saikhamhein/benchswitch-usb-dut-hub/PCB/models/nominal/SPZ1HM221G12O00RAXXX_nominal.step

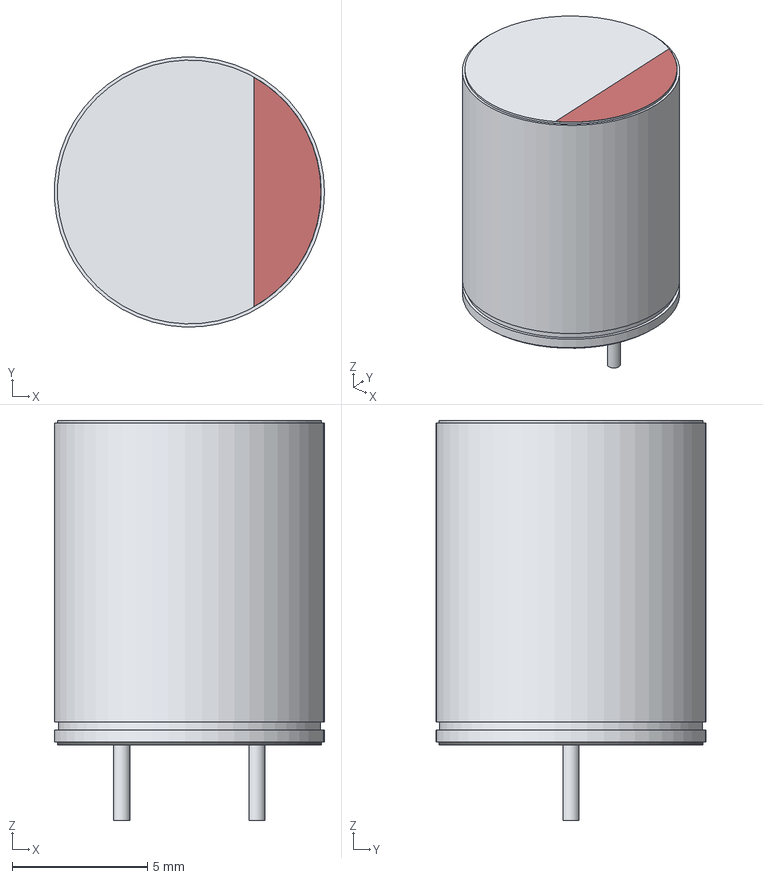
[picture p16: CAD file, 2026-10-05]
PCB/models/nominal/SPZ1HM221G12O00RAXXX_nominal.step
9.99 x 10.00 x 14.8 mm
Aluminum_can
Bottom_bung
Top_lid
Negative_polarity_red_sector
Lead_1_positive
Lead_2_negative
