saikhamhein/benchswitch-usb-dut-hub/PCB/models/nominal/XL1EL89CSI_111YLC_24M_nominal.step

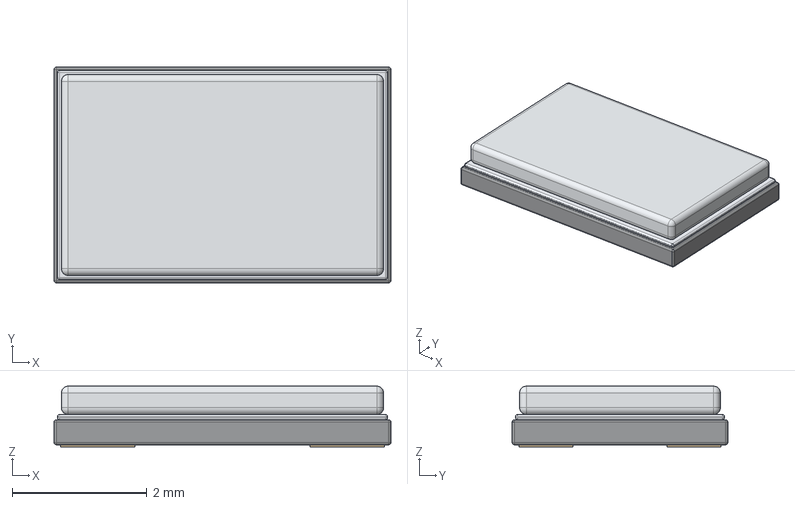
[picture p17: CAD file, 2026-10-05]
PCB/models/nominal/XL1EL89CSI_111YLC_24M_nominal.step
5.00 x 3.20 x 0.9 mm
Ceramic_base
Metal_sealing_flange
Metal_lid_no_text
Gold_terminal_1
Gold_terminal_2
Gold_terminal_3
Gold_terminal_4
