saikhamhein/benchswitch-usb-dut-hub/PCB/models/nominal/CL10C330JB8NNNC_nominal.step

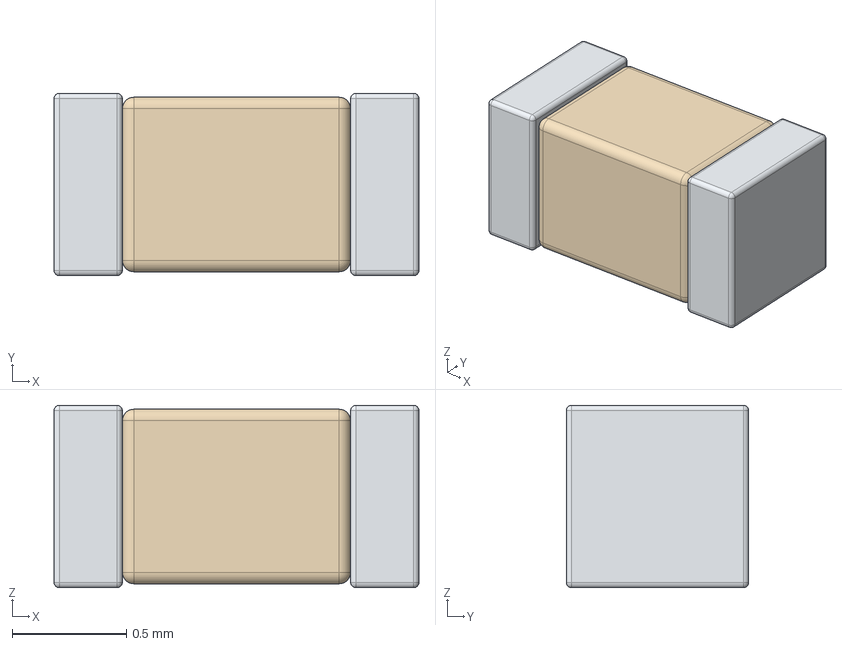
[picture p18: CAD file, 2026-10-05]
PCB/models/nominal/CL10C330JB8NNNC_nominal.step
1.60 x 0.8 x 0.8 mm
Ceramic_nominal
Termination_1
Termination_2
