saikhamhein/benchswitch-usb-dut-hub/PCB/models/nominal/MNR8065T100MT_nominal.step

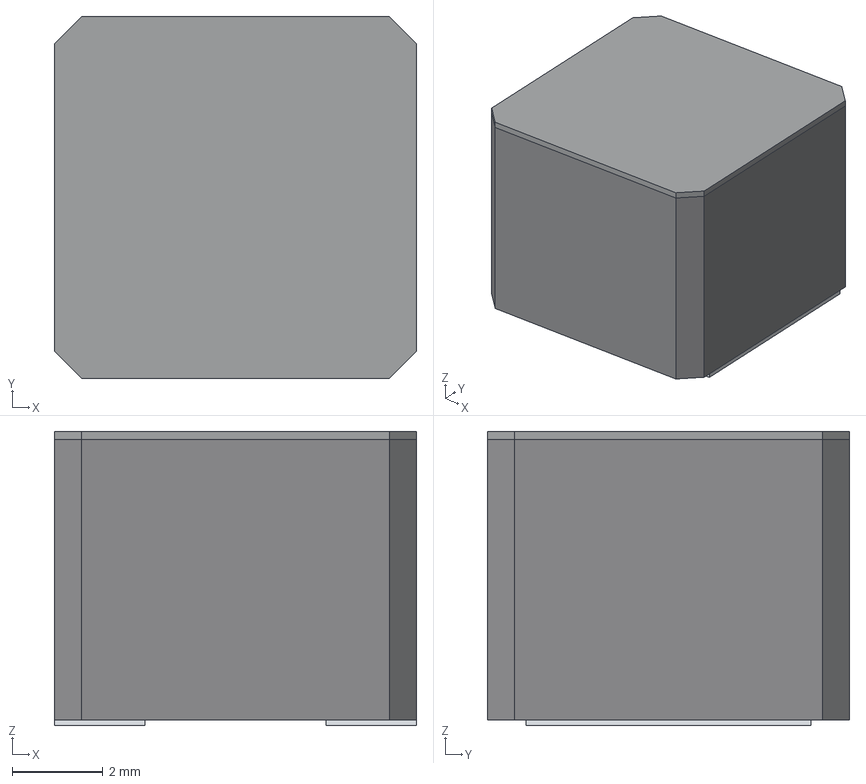
[picture p19: CAD file, 2026-10-05]
PCB/models/nominal/MNR8065T100MT_nominal.step
8.00 x 8.00 x 6.50 mm
Magnetic_resin_body_nominal_XY_max_H
Ferrite_top_face
Tin_terminal_1
Tin_terminal_2
