saikhamhein/benchswitch-usb-dut-hub/PCB/models/nominal/RC0603_RT0603_nominal.step

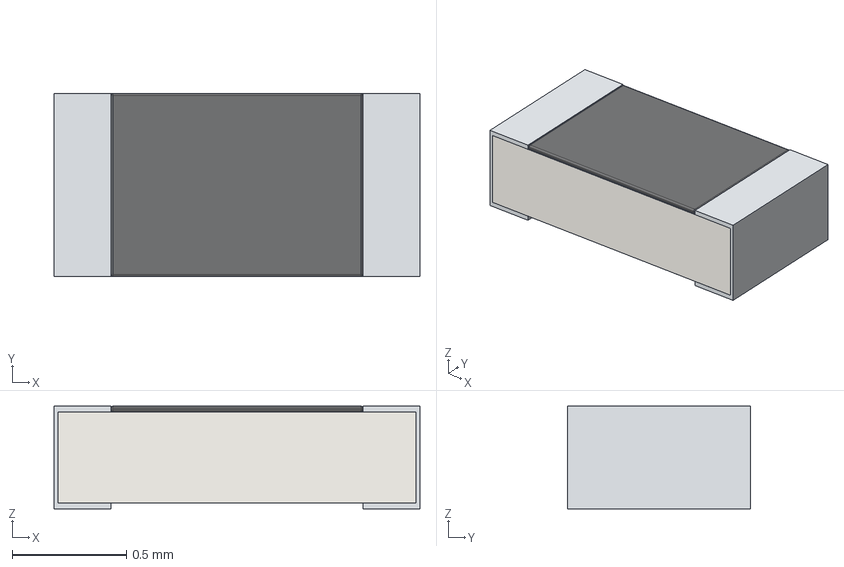
[picture p20: CAD file, 2026-10-05]
PCB/models/nominal/RC0603_RT0603_nominal.step
1.60 x 0.8 x 0.45 mm
Alumina_substrate
Resistive_overcoat_no_text
Termination_1
Termination_2
