saikhamhein/benchswitch-usb-dut-hub/PCB/models/nominal/CH217A_family_nominal.step

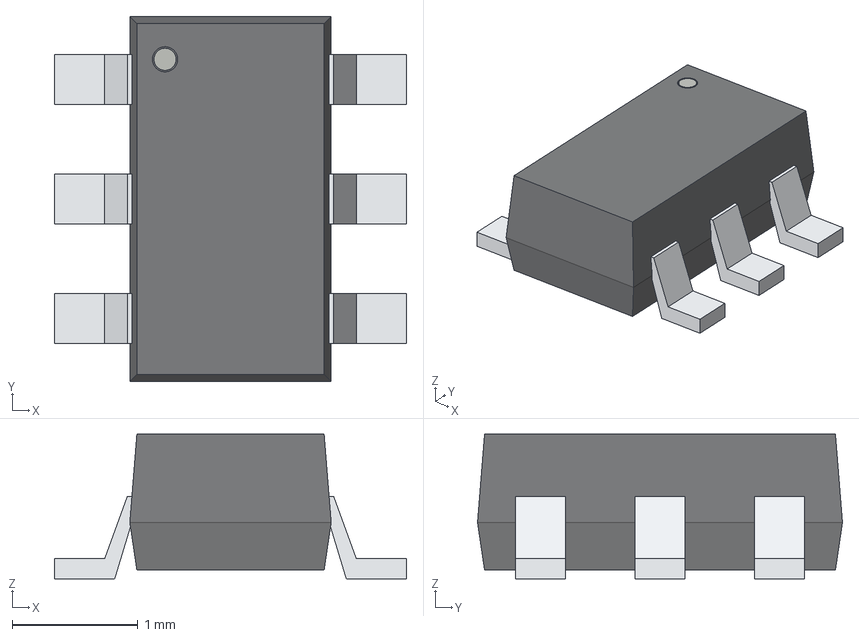
[picture p21: CAD file, 2026-10-05]
PCB/models/nominal/CH217A_family_nominal.step
2.80 x 2.90 x 1.15 mm
Pin1_orientation_dot_schematic
Molded_body
Lead_1
Lead_2
Lead_3
Lead_4
Lead_5
Lead_6
