saikhamhein/benchswitch-usb-dut-hub/PCB/models/nominal/CC0805KKX7R7BB106_nominal.step

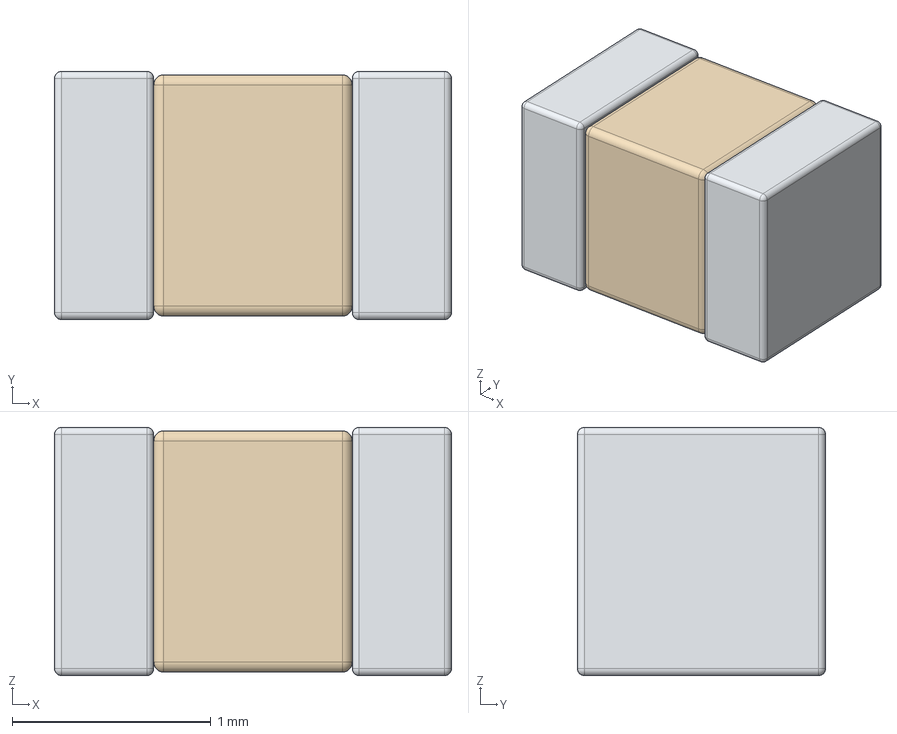
[picture p22: CAD file, 2026-10-05]
PCB/models/nominal/CC0805KKX7R7BB106_nominal.step
2.00 x 1.25 x 1.25 mm
Ceramic_nominal
Termination_1
Termination_2
