saikhamhein/benchswitch-usb-dut-hub/PCB/models/nominal/LTST_S270KGKT_sideview_nominal.step

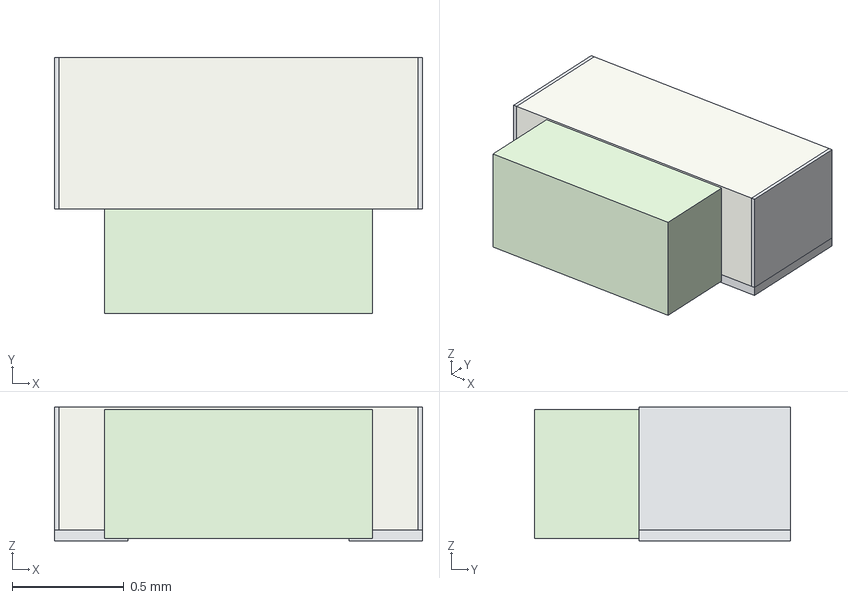
[picture p23: CAD file, 2026-10-05]
PCB/models/nominal/LTST_S270KGKT_sideview_nominal.step
1.65 x 1.15 x 0.6 mm
Ceramic_package
Cathode_1
Cathode_end
Anode_2
Anode_end
Water_clear_side_lens
Green_die_behind_lens
Cathode_underside_mark
