saikhamhein/benchswitch-usb-dut-hub/PCB/models/nominal/USB2514B_AEZC_QFN36_nominal.step

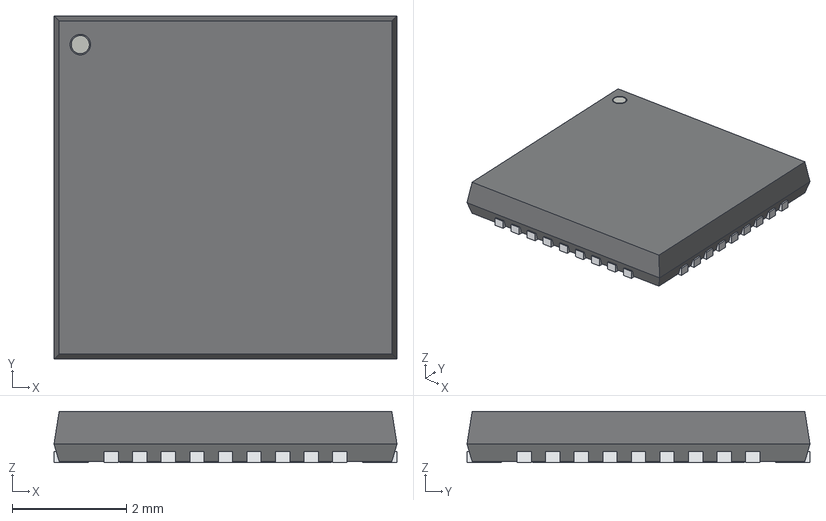
[picture p24: CAD file, 2026-10-05]
PCB/models/nominal/USB2514B_AEZC_QFN36_nominal.step
6.00 x 6.00 x 0.9 mm
Pin1_orientation_dot_schematic
Molded_body
Exposed_pad_37
Terminal_1
Terminal_10
Terminal_19
Terminal_28
Terminal_2
Terminal_11
Terminal_20
Terminal_29
Terminal_3
Terminal_12
Terminal_21
Terminal_30
Terminal_4
Terminal_13
Terminal_22
Terminal_31
Terminal_5
Terminal_14
Terminal_23
Terminal_32
Terminal_6
Terminal_15
Terminal_24
Terminal_33
Terminal_7
Terminal_16
Terminal_25
Terminal_34
Terminal_8
Terminal_17
Terminal_26
Terminal_35
Terminal_9
Terminal_18
Terminal_27
Terminal_36
