saikhamhein/benchswitch-usb-dut-hub/PCB/models/nominal/ERS1AM221E11OT_nominal.step

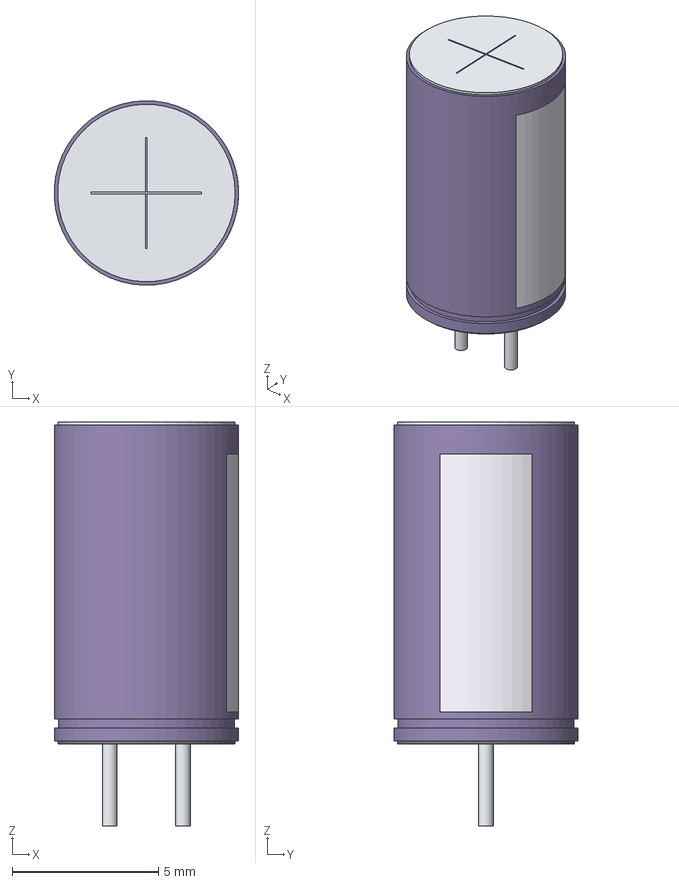
[picture p25: CAD file, 2026-10-05]
PCB/models/nominal/ERS1AM221E11OT_nominal.step
6.29 x 6.30 x 13.8 mm
Violet_sleeved_can
Bottom_bung
Top_lid
Negative_polarity_stripe
Lead_1_positive
Lead_2_negative
