saikhamhein/benchswitch-usb-dut-hub/PCB/models/nominal/CC0402KRX7R8BB104_nominal.step

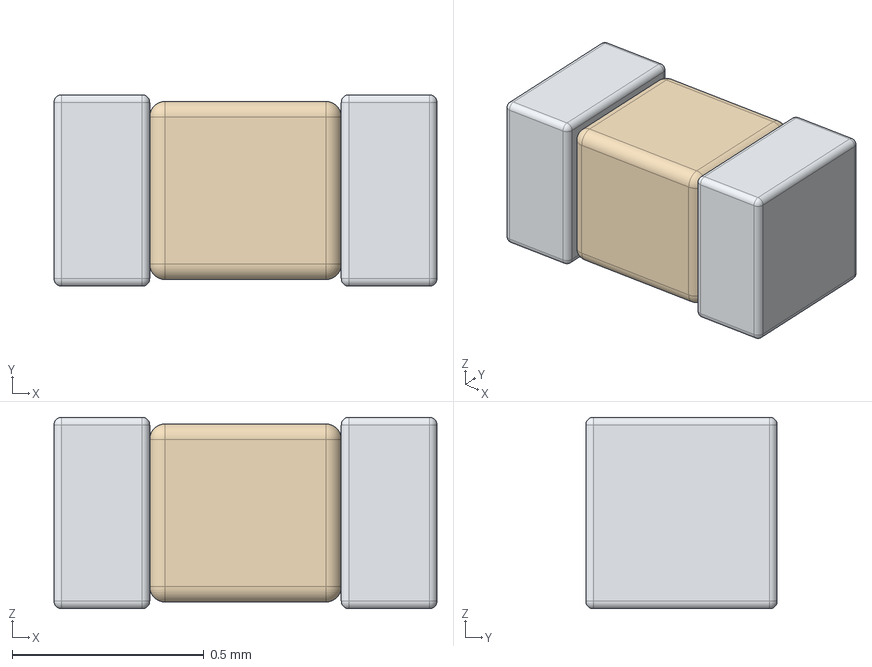
[picture p26: CAD file, 2026-10-05]
PCB/models/nominal/CC0402KRX7R8BB104_nominal.step
1.00 x 0.5 x 0.5 mm
Ceramic_nominal
Termination_1
Termination_2
