saikhamhein/benchswitch-usb-dut-hub/PCB/models/nominal/ETA7014S2G_nominal.step

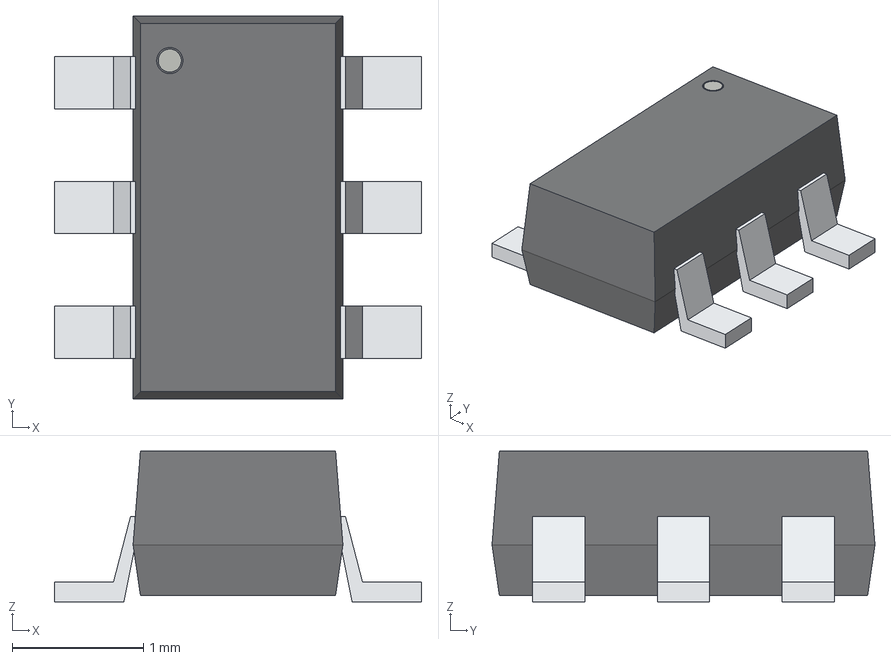
[picture p27: CAD file, 2026-10-05]
PCB/models/nominal/ETA7014S2G_nominal.step
2.80 x 2.92 x 1.15 mm
Pin1_orientation_dot_schematic
Molded_body
Lead_1
Lead_2
Lead_3
Lead_4
Lead_5
Lead_6
